antosiowsky/epaper-measurement-hub/EKRAN/wyświetlacz/wyświetlacz pcb.pdf

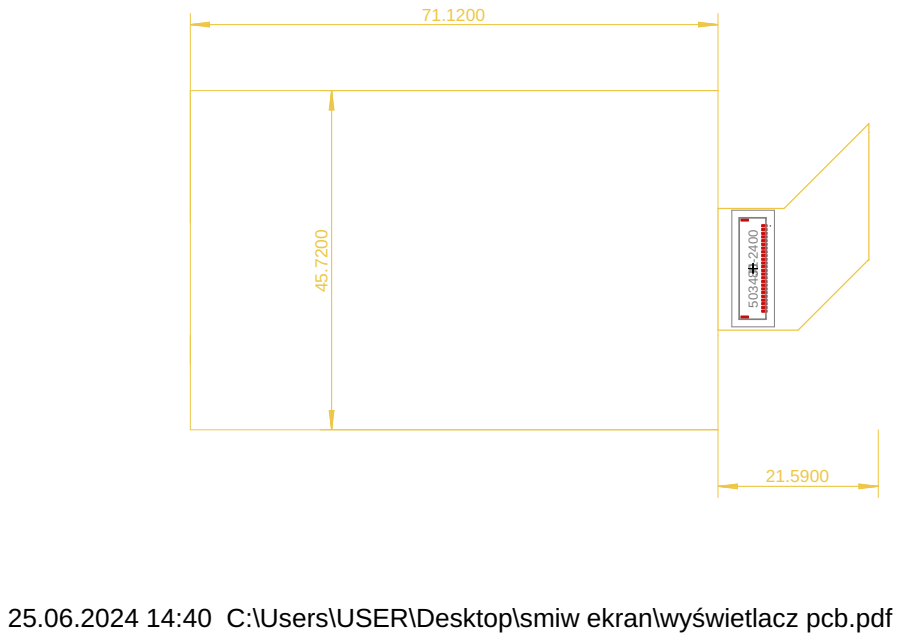
[picture p1: page 1]

25.06.2024 14:40 C:\Users\USER\Desktop\smiw ekran\wyświetlacz pcb.pdf
