antosiowsky/epaper-measurement-hub/PAMIĘĆ/PCB/Płytka PCB Fram Bottom.pdf

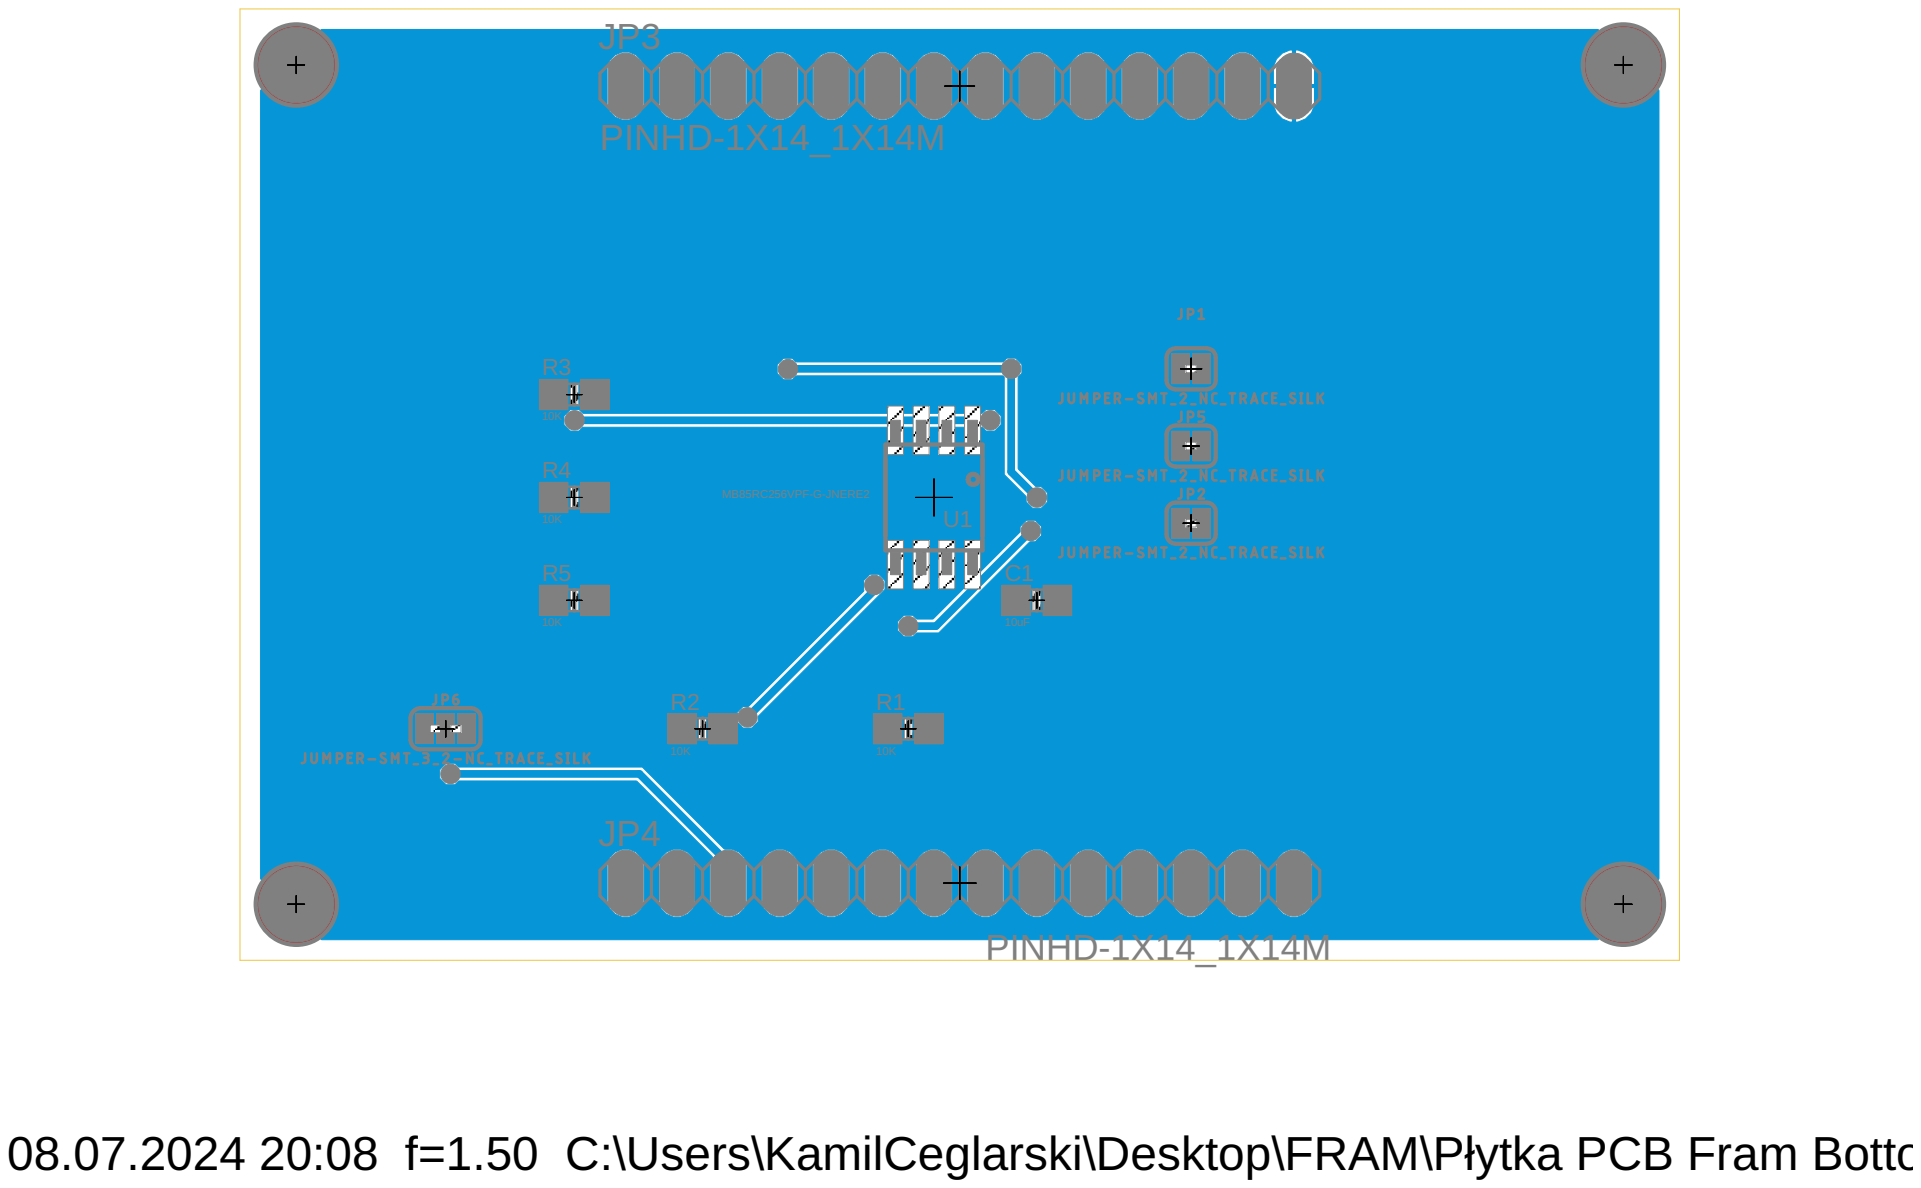
[picture p2: page 1]

08.07.2024 20:08 f=1.50 C:\Users\KamilCeglarski\Desktop\FRAM\Płytka PCB Fram Bottom.pdf
