antosiowsky/epaper-measurement-hub/PAMIĘĆ/PCB/Płytka PCB Fram Top.pdf

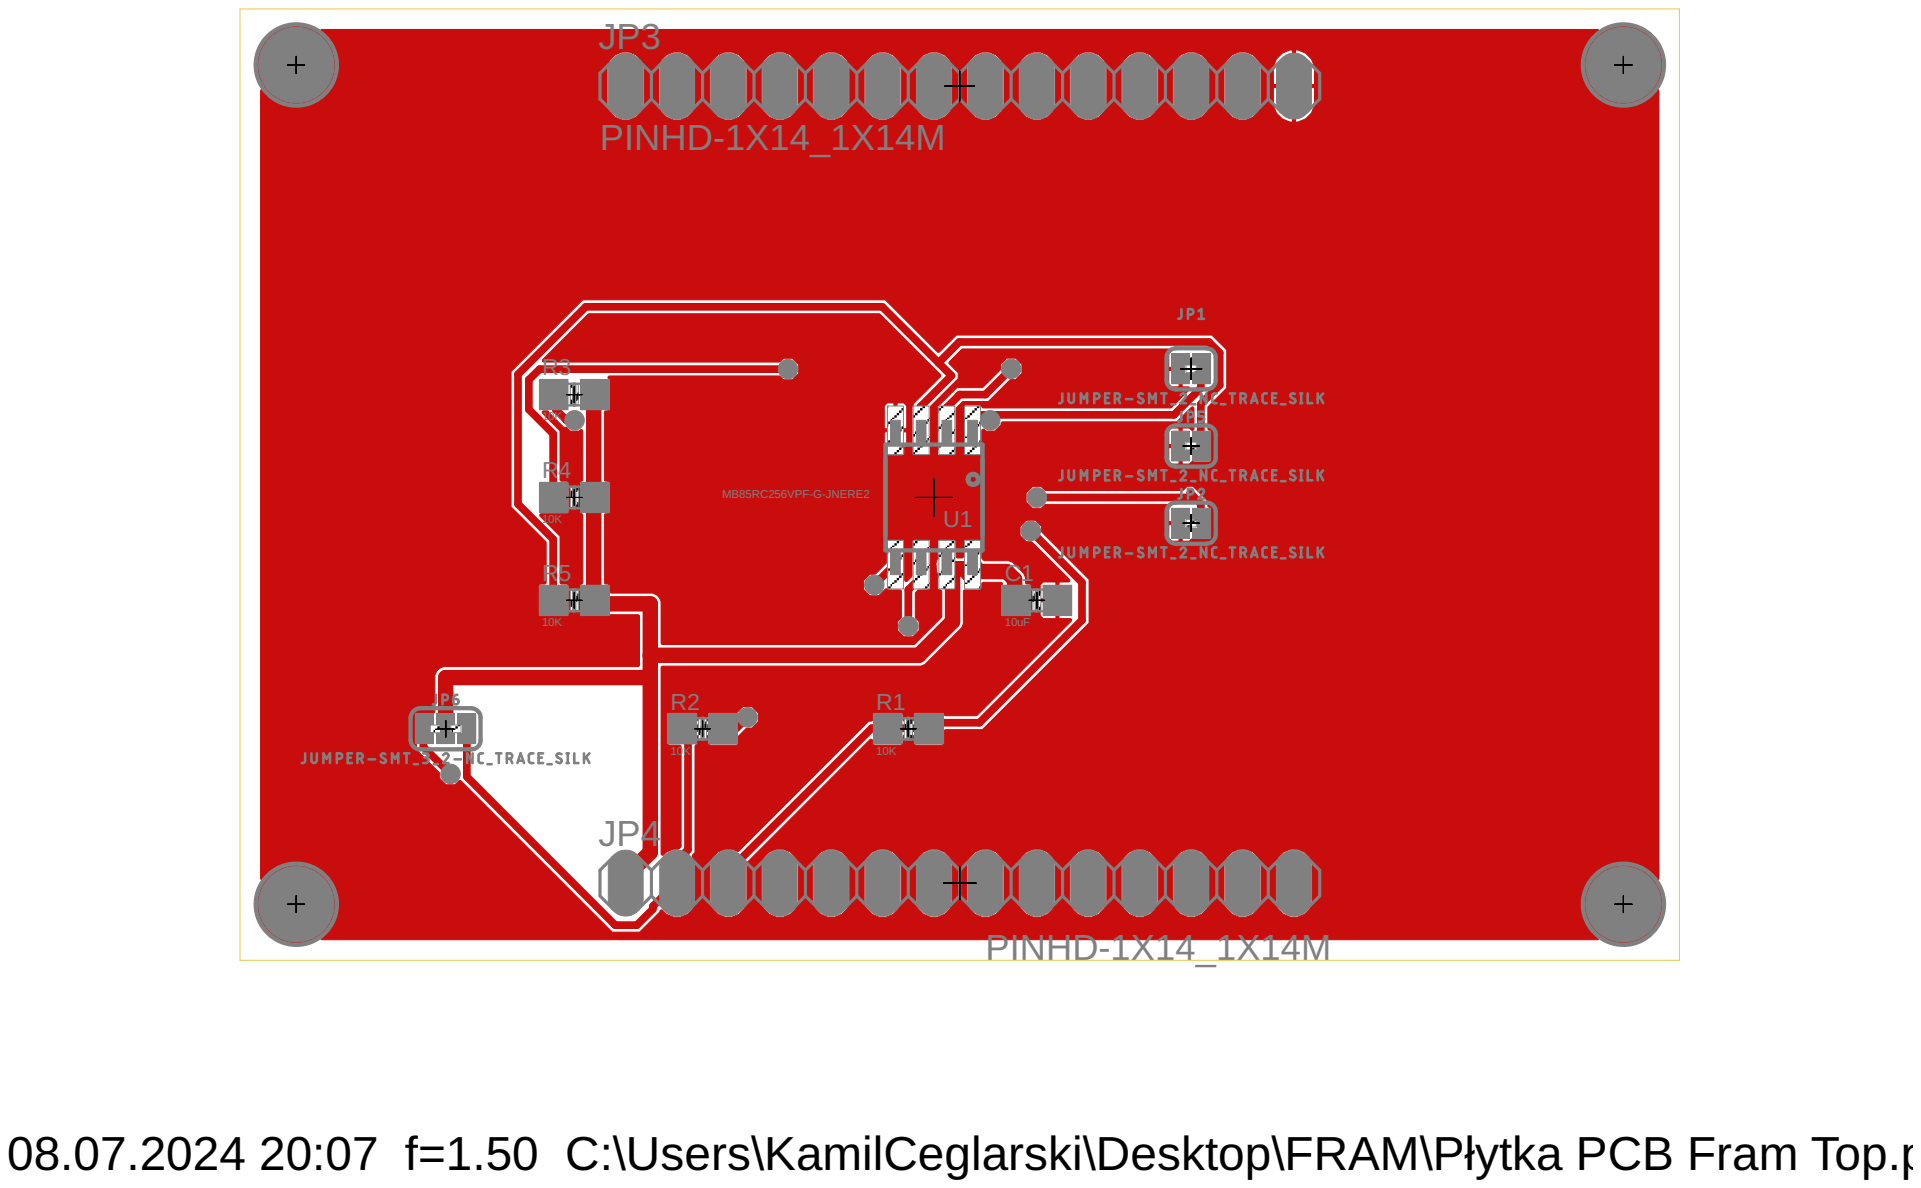
[picture p3: page 1]

08.07.2024 20:07 f=1.50 C:\Users\KamilCeglarski\Desktop\FRAM\Płytka PCB Fram Top.pdf
