antosiowsky/epaper-measurement-hub/PAMIĘĆ/PCB/Płytka PCB Fram Top_BezMasy.pdf

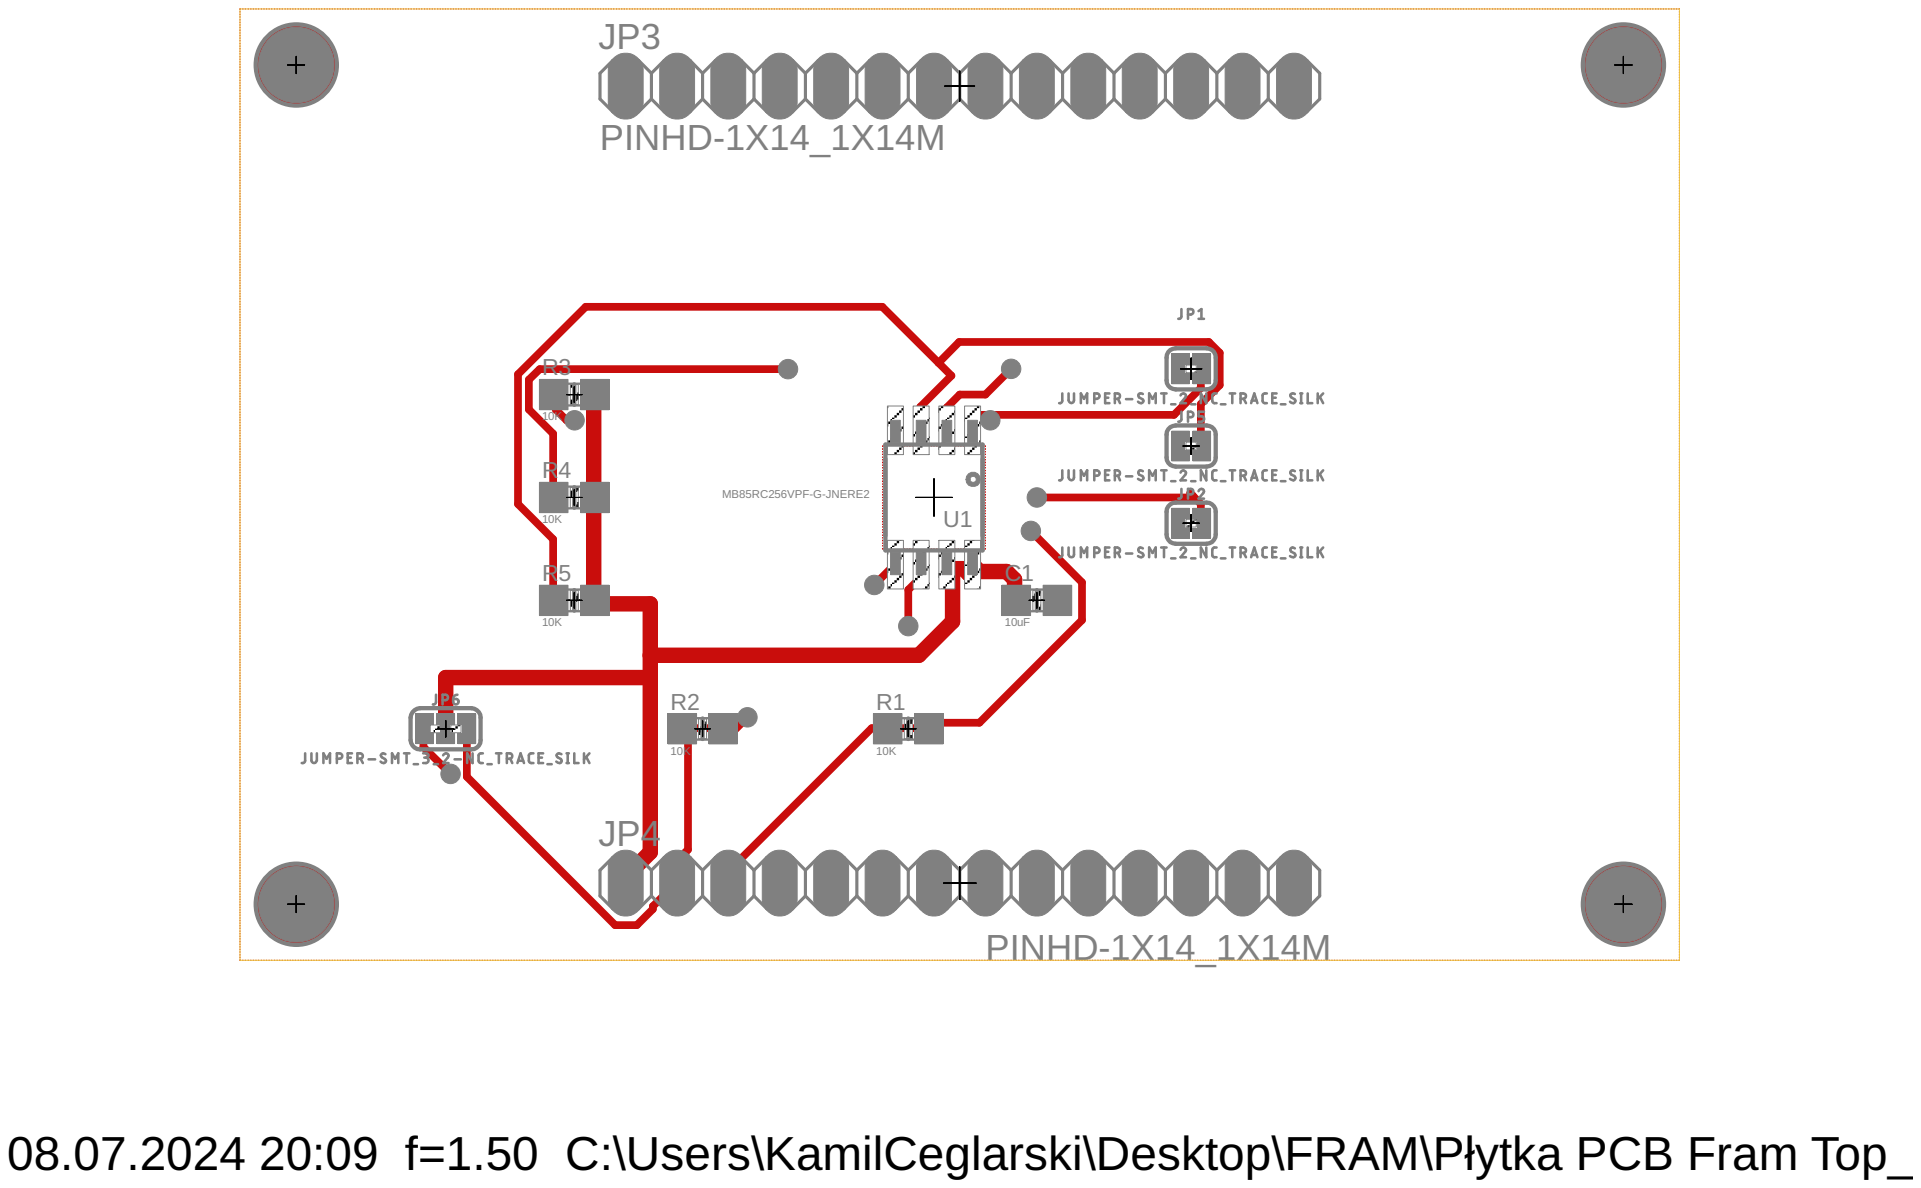
[picture p4: page 1]

08.07.2024 20:09 f=1.50 C:\Users\KamilCeglarski\Desktop\FRAM\Płytka PCB Fram Top_BezMasy.pdf
