antosiowsky/epaper-measurement-hub/PAMIĘĆ/PCB/Płytka PCB Fram Top_Bottom.pdf

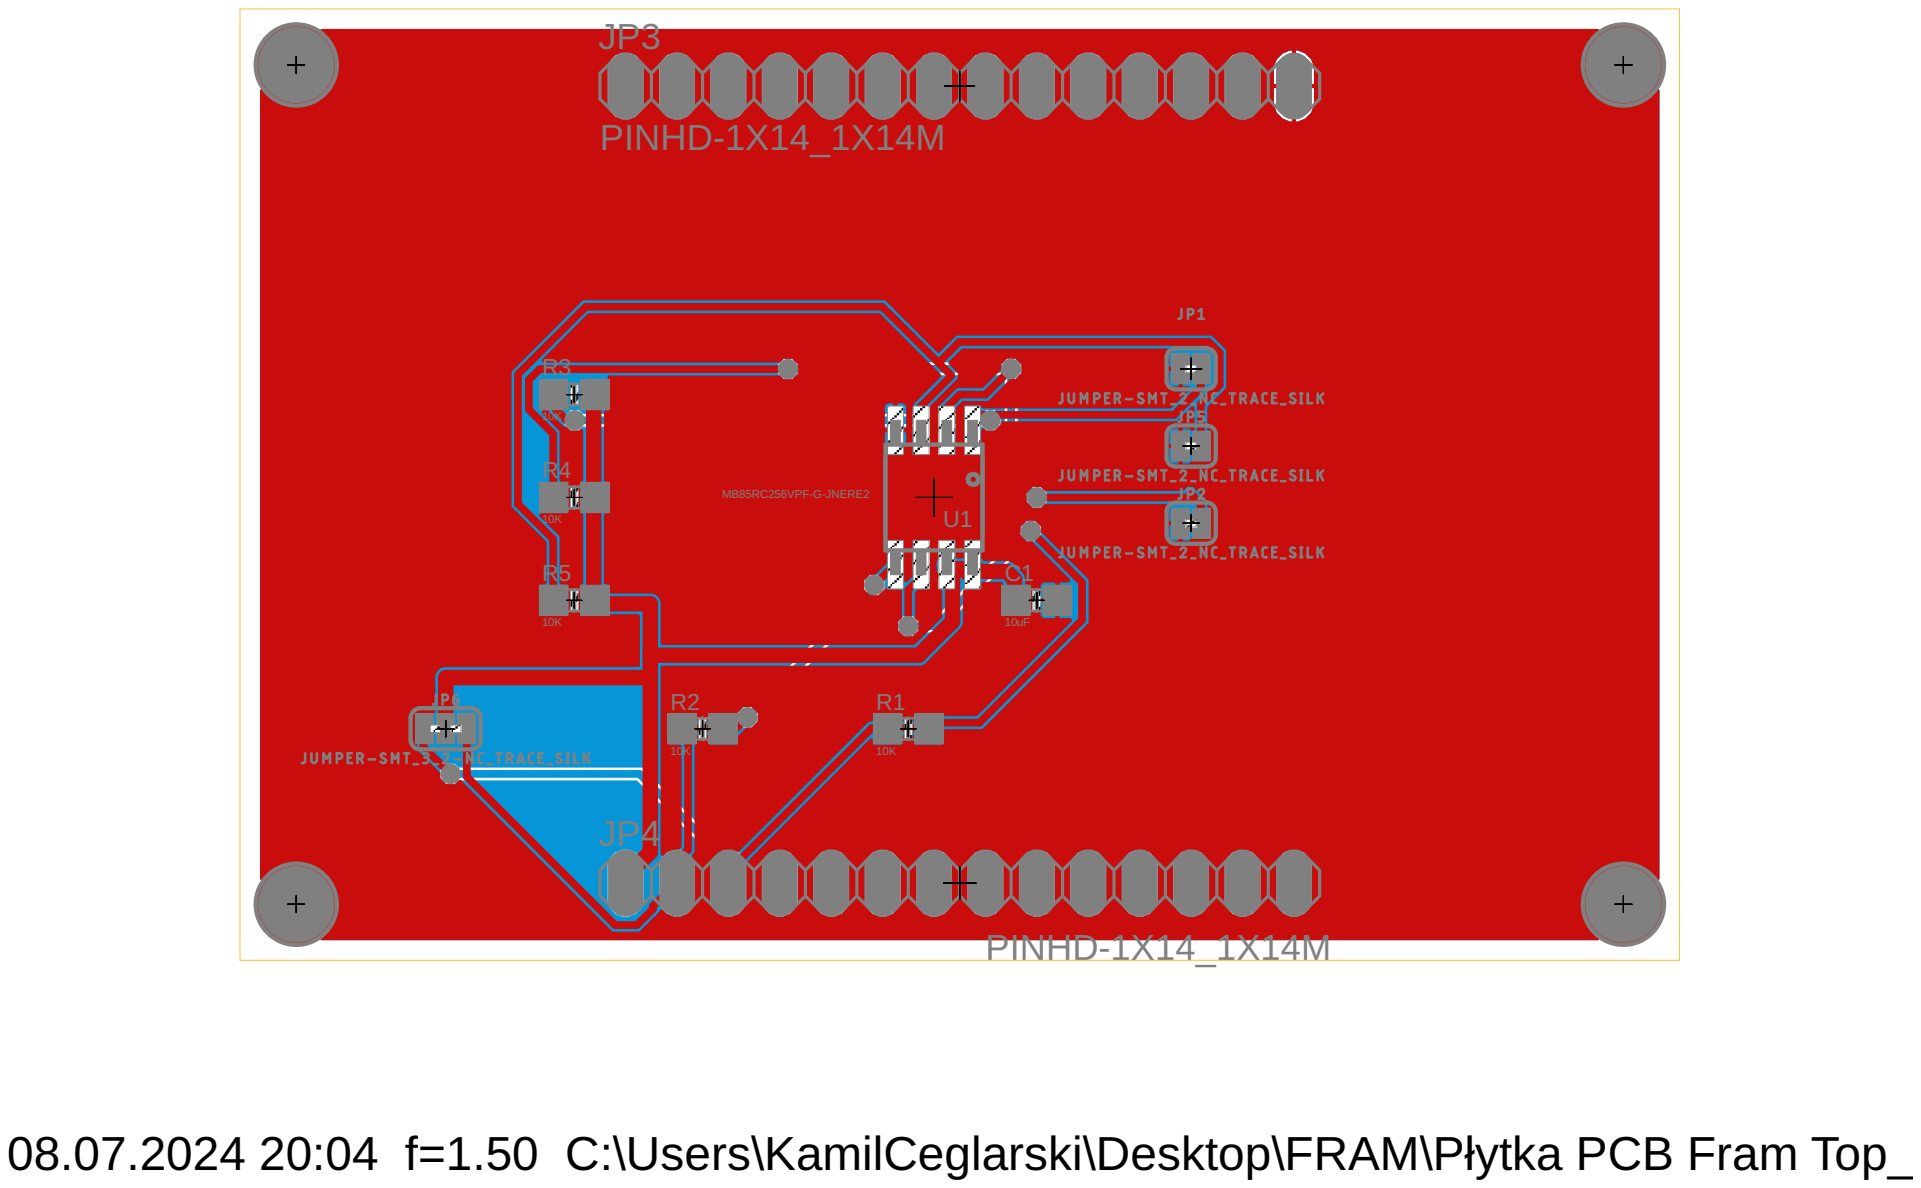
[picture p5: page 1]

08.07.2024 20:04 f=1.50 C:\Users\KamilCeglarski\Desktop\FRAM\Płytka PCB Fram Top_Bottom.pdf
