antosiowsky/epaper-measurement-hub/EKRAN/Ekran/Ekran_masa_bottom.pdf

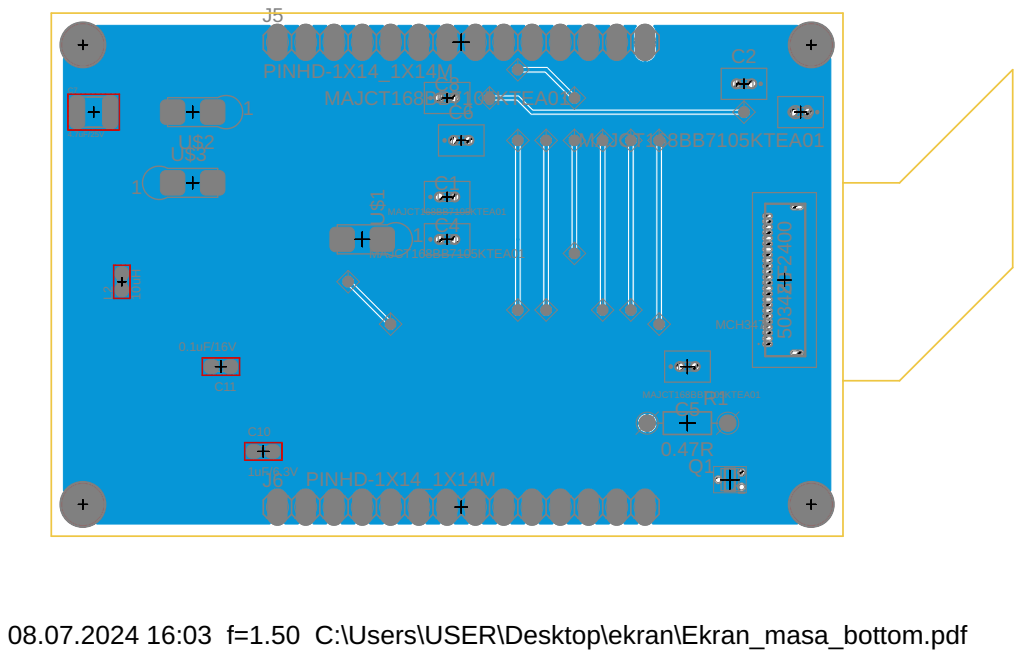
[picture p18: page 1]

08.07.2024 16:03 f=1.50 C:\Users\USER\Desktop\ekran\Ekran_masa_bottom.pdf
