antosiowsky/epaper-measurement-hub/EKRAN/Ekran/Ekran_masa_top&bottom.pdf

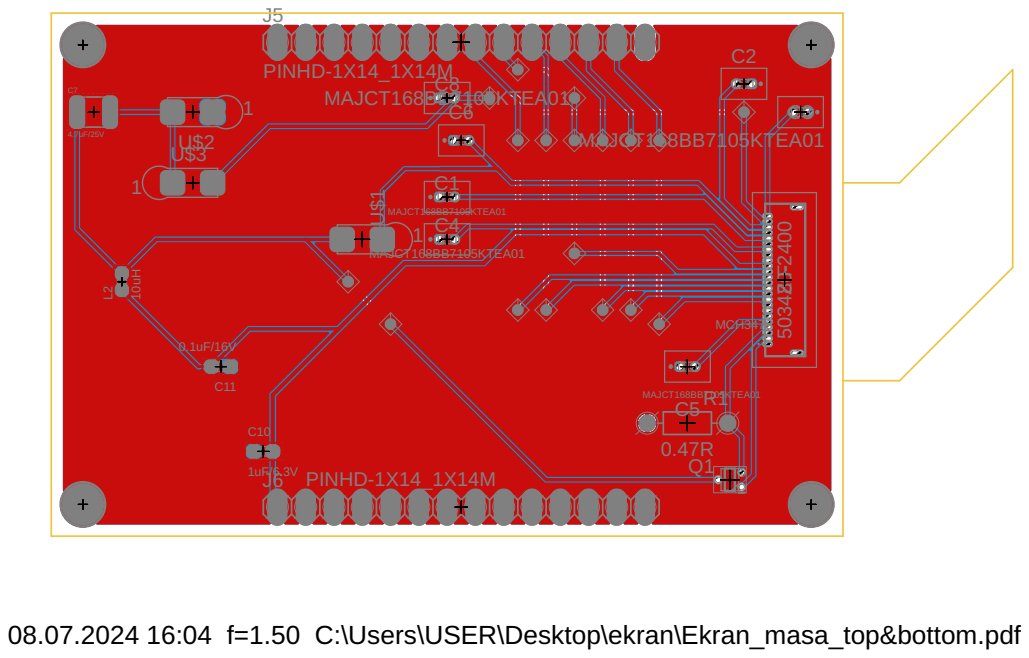
[picture p19: page 1]

08.07.2024 16:04 f=1.50 C:\Users\USER\Desktop\ekran\Ekran_masa_top&bottom.pdf
