antosiowsky/epaper-measurement-hub/PROCESOR/PCB/bottom_bez_masy.pdf

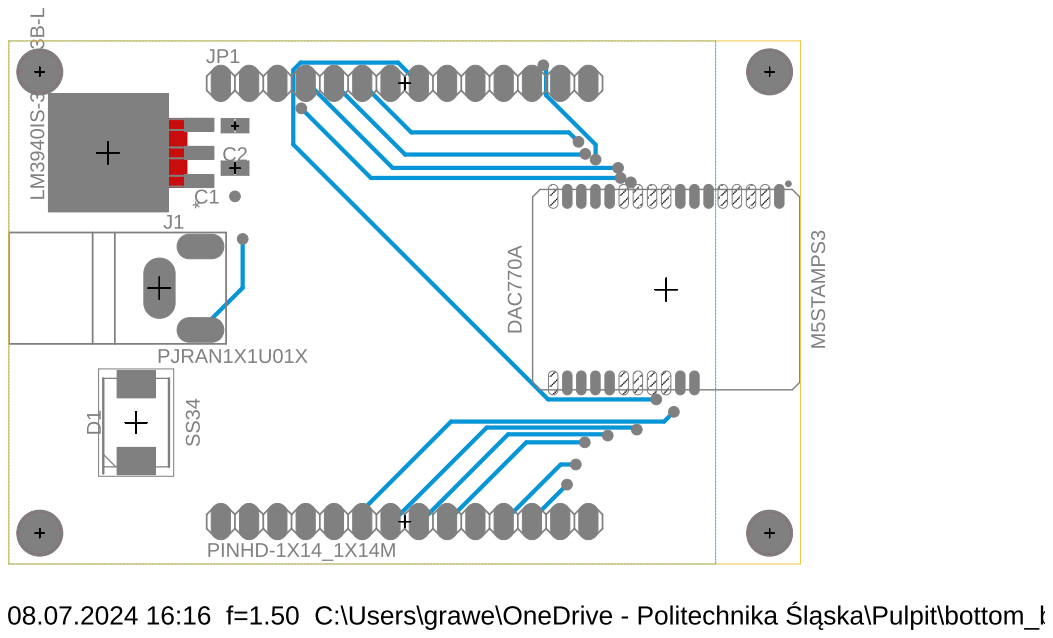
[picture p21: page 1]
