antosiowsky/epaper-measurement-hub/PROCESOR/PCB/bottom_masa.pdf

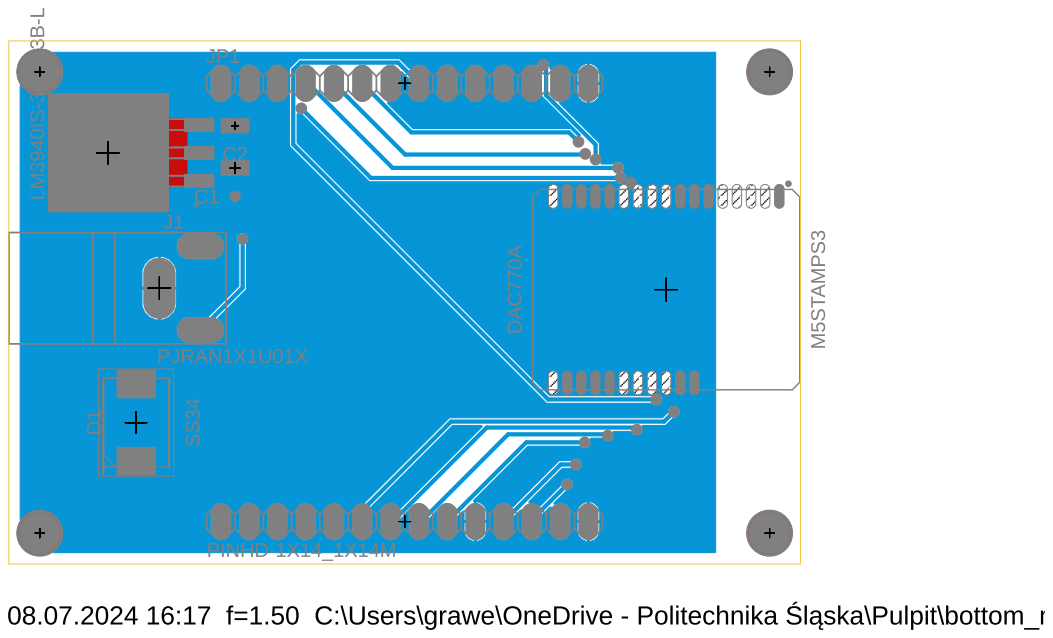
[picture p22: page 1]
