antosiowsky/epaper-measurement-hub/PROCESOR/PCB/top_bez_masy.pdf

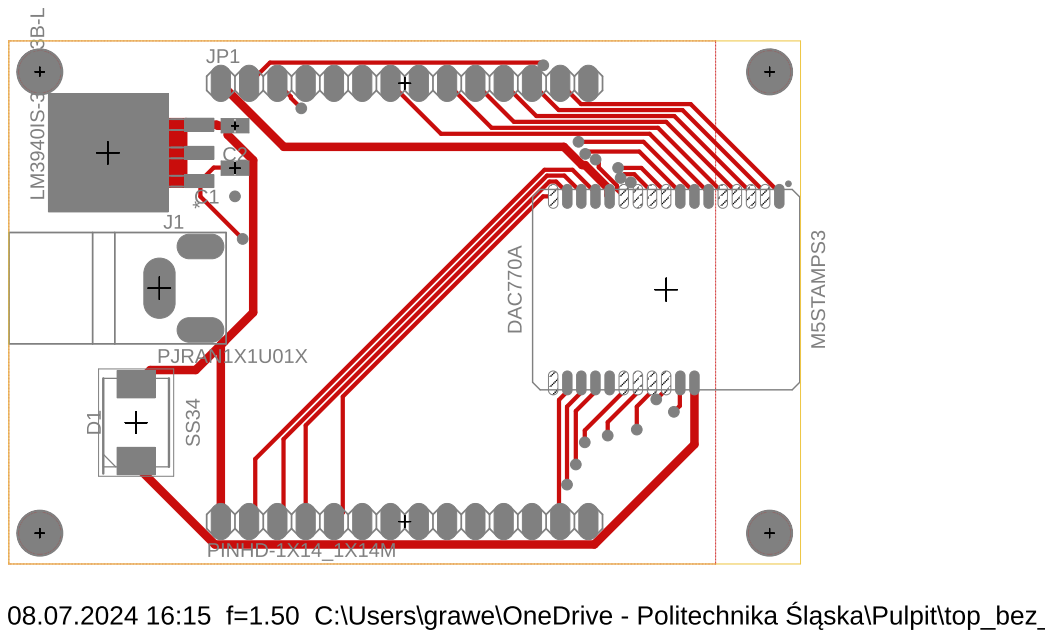
[picture p23: page 1]
