antosiowsky/epaper-measurement-hub/PROCESOR/PCB/top_bottom_bez_masy.pdf

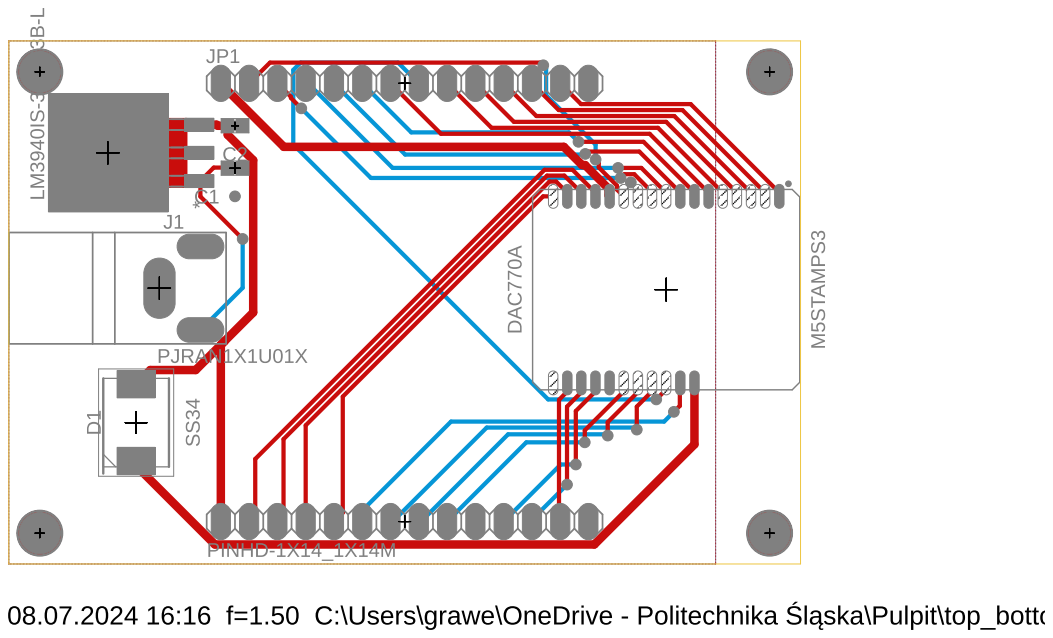
[picture p24: page 1]
