antosiowsky/epaper-measurement-hub/PROCESOR/PCB/top_masa.pdf

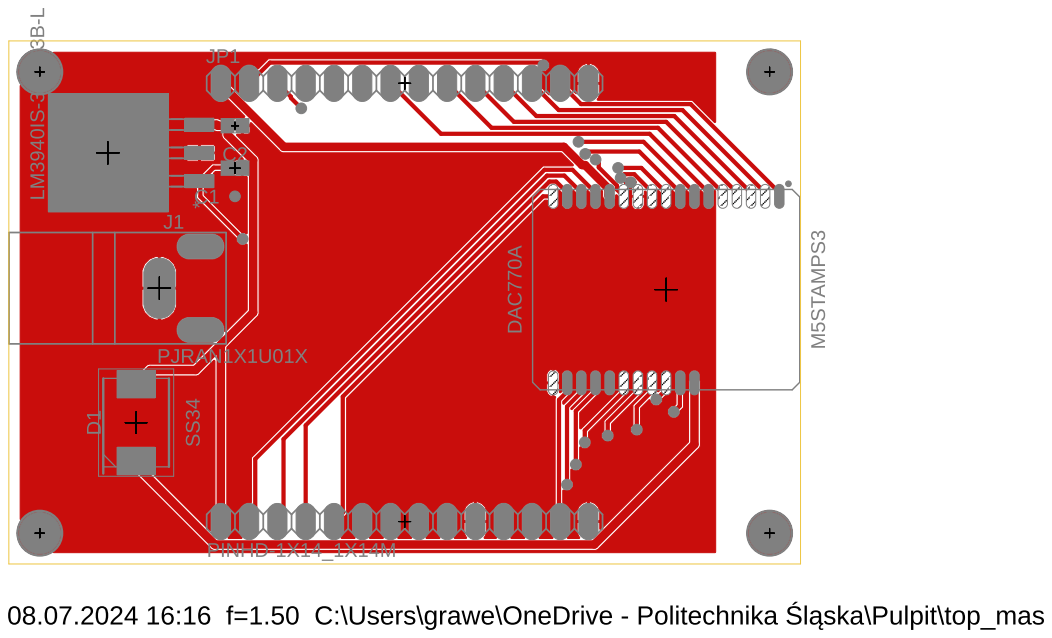
[picture p25: page 1]
